coreyhhowell/Circuit-Workers-Congress/panda.h

// array size is 182750
static const unsigned char panda[] PROGMEM  = {
   0x89, 0x50, 0x4e, 0x47, 0x0d, 0x0a, 0x1a, 0x0a, 0x00, 0x00, 0x00, 0x0d, 0x49, 0x48, 0x44, 0x52, 
  0x00, 0x00, 0x00, 0xe7, 0x00, 0x00, 0x00, 0xe7, 0x08, 0x02, 0x00, 0x00, 0x00, 0x6a, 0x96, 0xd6, 
  0x77, 0x00, 0x00, 0x00, 0x06, 0x62, 0x4b, 0x47, 0x44, 0x00, 0xff, 0x00, 0xff, 0x00, 0xff, 0xa0, 
  0xbd, 0xa7, 0x93, 0x00, 0x00, 0x04, 0xe2, 0x49, 0x44, 0x41, 0x54, 0x78, 0x9c, 0xed, 0xdd, 0x41, 
  0x4e, 0x2b, 0x39, 0x14, 0x40, 0x51, 0x68, 0xfd, 0x55, 0x65, 0x29, 0x6c, 0x81, 0xf5, 0xb0, 0xa5, 
  0x6c, 0x8b, 0x1e, 0xf4, 0x34, 0x1f, 0x39, 0x6d, 0xec, 0xf2, 0x85, 0x73, 0xc6, 0x24, 0x29, 0xc8, 
  0x95, 0x85, 0x9e, 0x5c, 0xae, 0xd7, 0xcf, 0xcf, 0xcf, 0x17, 0x48, 0xf9, 0xe7, 0xea, 0x0b, 0x80, 
  0xa7, 0xa9, 0x96, 0x1e, 0xd5, 0xd2, 0xa3, 0x5a, 0x7a, 0x54, 0x4b, 0x8f, 0x6a, 0xe9, 0x51, 0x2d, 
  0x3d, 0xaa, 0xa5, 0x47, 0xb5, 0xf4, 0xa8, 0x96, 0x1e, 0xd5, 0xd2, 0xa3, 0x5a, 0x7a, 0x54, 0x4b, 
  0xcf, 0x9f, 0xf1, 0x1f, 0x7d, 0x7d, 0x7d, 0x5d, 0x77, 0x1d, 0xff, 0xcf, 0xf8, 0x86, 0xb5, 0x87, 
  0x17, 0xff, 0xf0, 0xe5, 0xe3, 0x3f, 0x39, 0x6e, 0xfc, 0x4f, 0x77, 0xe0, 0x25, 0x6d, 0x33, 0xfe, 
  0x1b, 0x59, 0x6b, 0xe9, 0x51, 0x2d, 0x3d, 0xaa, 0xa5, 0x47, 0xb5, 0xf4, 0xa8, 0x96, 0x1e, 0xd5, 
  0xd2, 0xf3, 0xc4, 0xe4, 0xeb, 0xa1, 0xf7, 0xf7, 0xf7, 0xdb, 0xed, 0xf6, 0x2d, 0x97, 0xf2, 0x85, 
  0xfb, 0xfd, 0xfe, 0xf1, 0xf1, 0x31, 0xf8, 0xc3, 0x93, 0x33, 0x9d, 0xc9, 0x69, 0xda, 0xf8, 0x7b, 
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
  0x7a, 0x54, 0x4b, 0x8f, 0x6a, 0xe9, 0x51, 0x2d, 0x3d, 0x4b, 0xce, 0xf9, 0xba, 0x76, 0x7f, 0xd6, 
  0x43, 0xdb, 0x86, 0x47, 0xd7, 0xde, 0x06, 0xb8, 0xe2, 0x3b, 0xda, 0x36, 0xcb, 0xf3, 0x6c, 0x47, 
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
};
